ApexHAB/apex-iii/core/pcb/rev1.0/apex-iii-core-brd.png

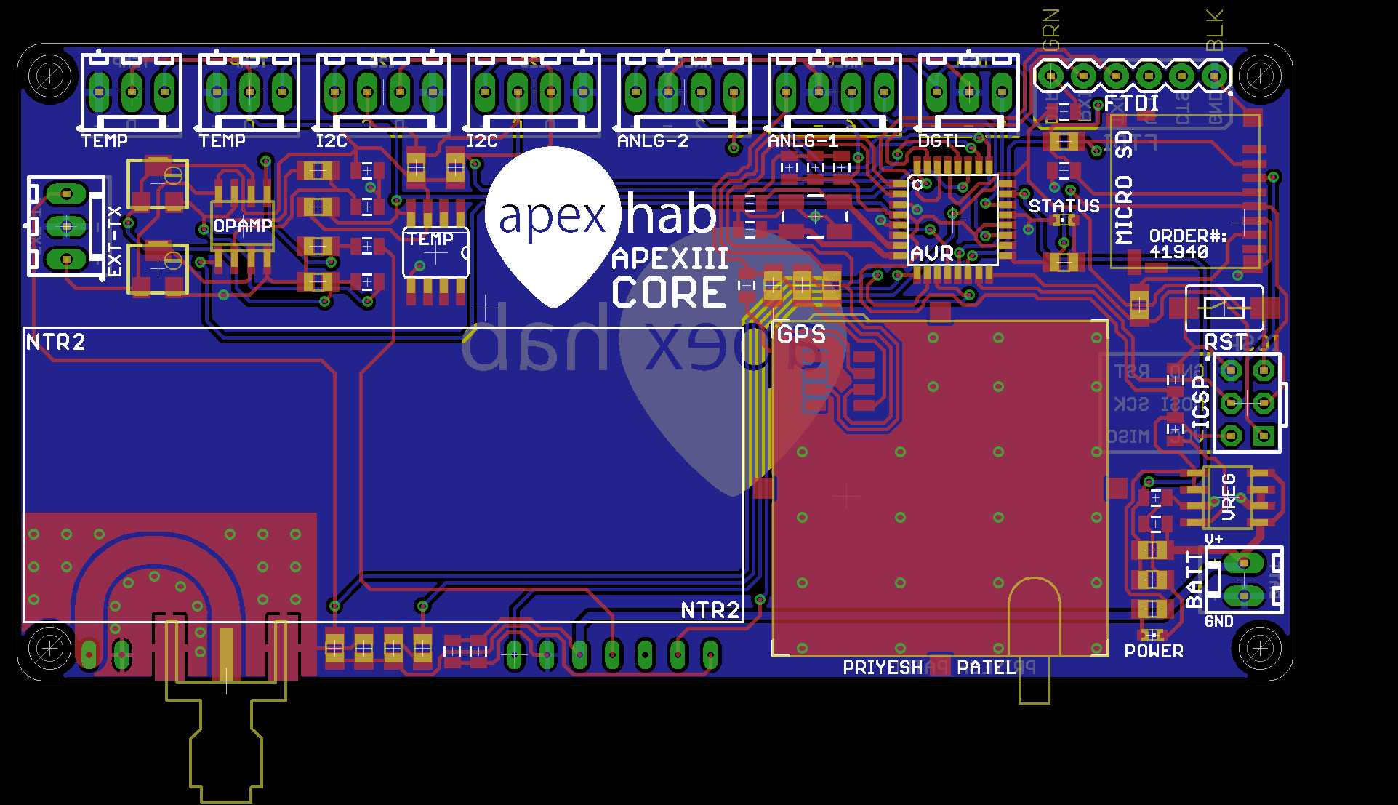
core/pcb/rev1.0/apex-iii-core-brd.png
