ApexHAB/apex-iii/core/pcb/rev1.0/apex-iii-core-sch.png

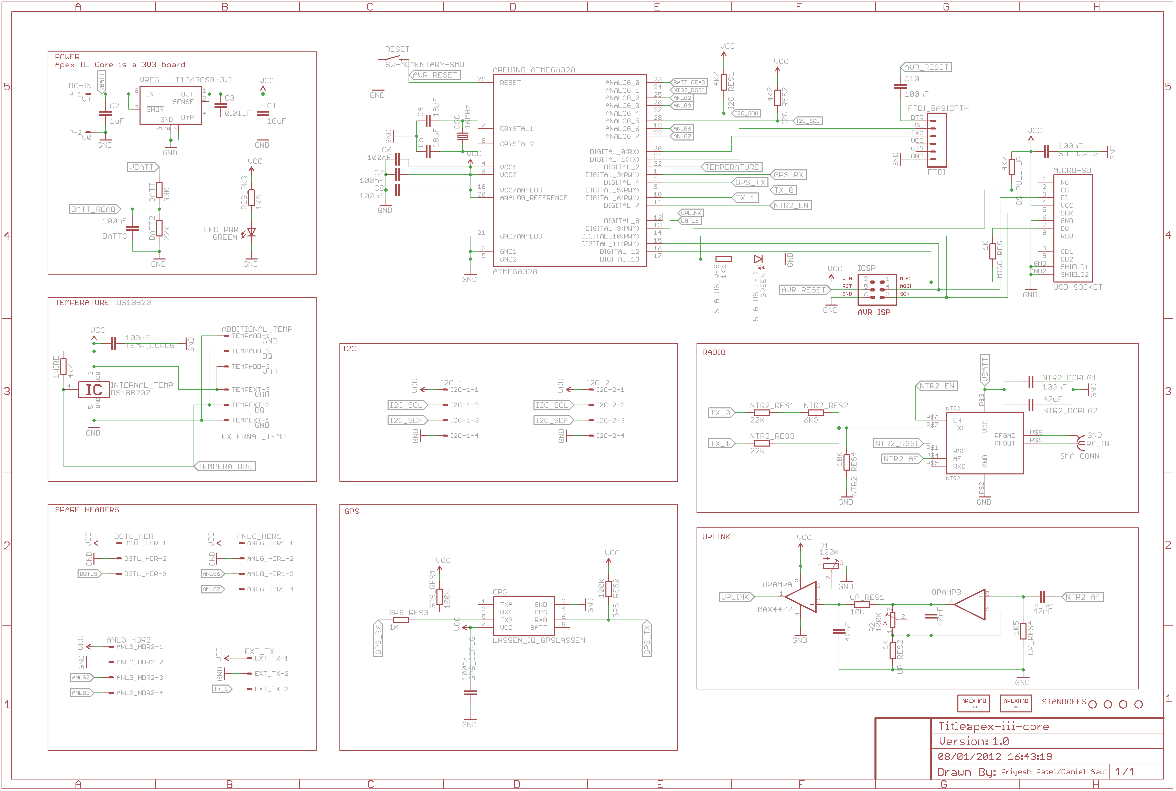
core/pcb/rev1.0/apex-iii-core-sch.png
