ApexHAB/apex-iii/launches/launch-1/track/apex-iii-l1-track-1.png

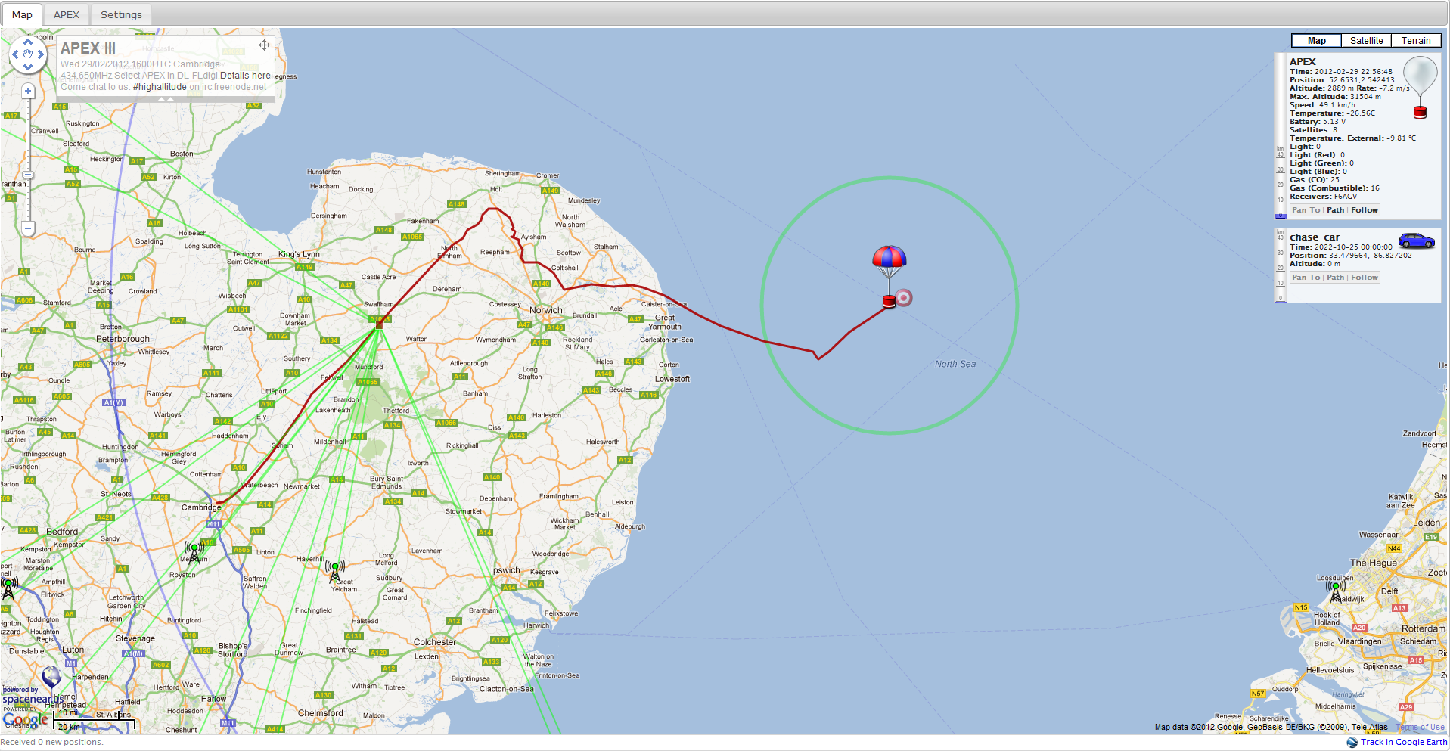
launches/launch-1/track/apex-iii-l1-track-1.png
