ApexHAB/apex-iii/launches/launch-1/track/apex-iii-l1-track-5.png

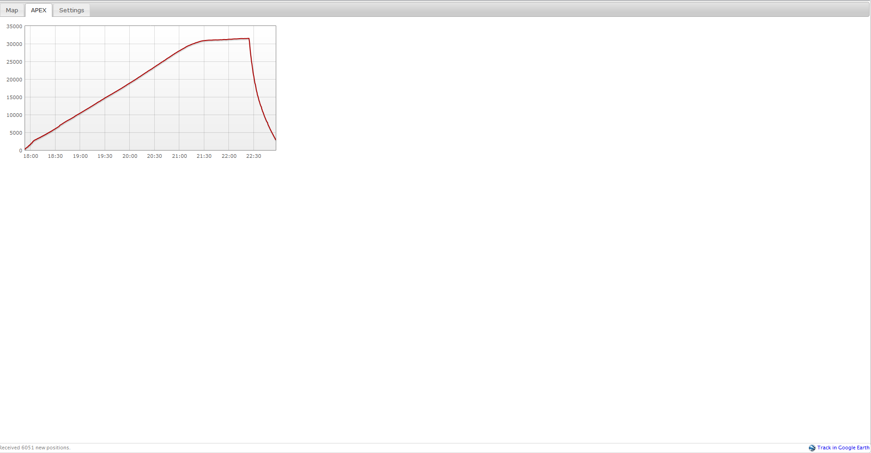
launches/launch-1/track/apex-iii-l1-track-5.png
