ApexHAB/apex-iii/launches/launch-2/track/ApexIIILaunch2-Track (2).png

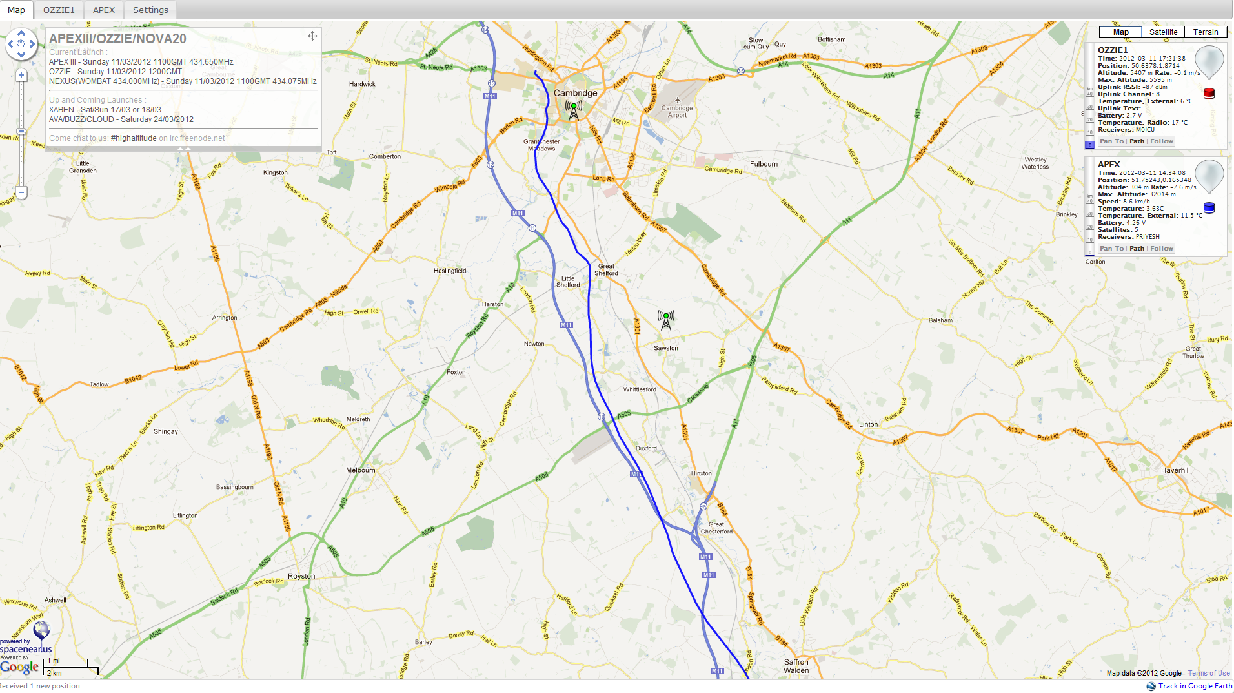
launches/launch-2/track/ApexIIILaunch2-Track (2).png
