ApexHAB/apex-iii/modules/adc_lemon/pcb/adc-lemon-sch.png

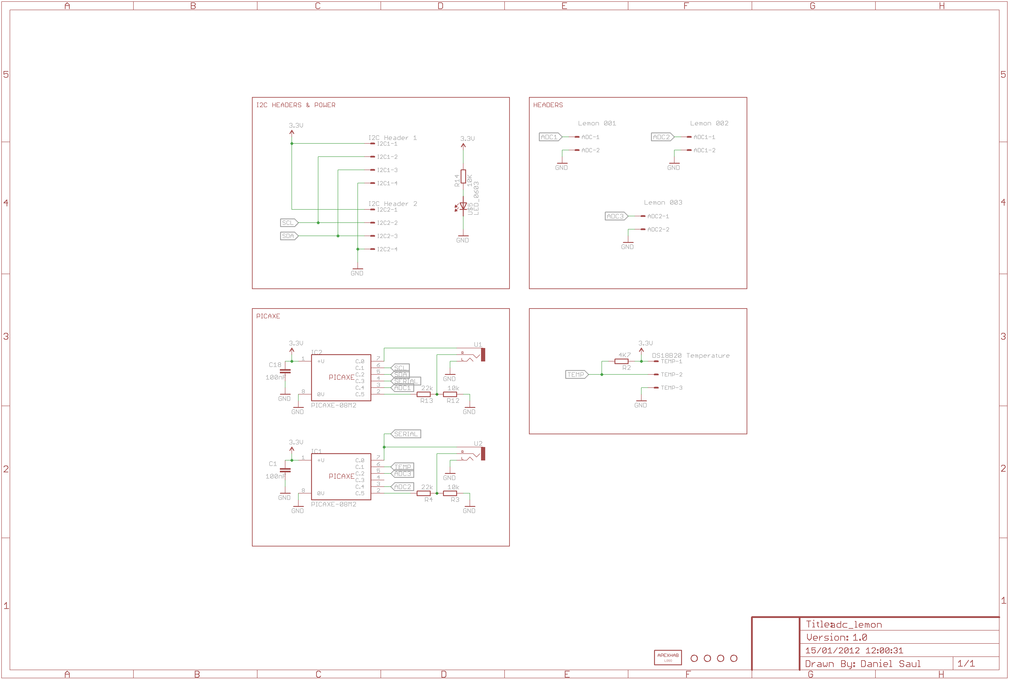
modules/adc_lemon/pcb/adc-lemon-sch.png
