ApexHAB/apex-iii/modules/light/pcb/light-brd.png

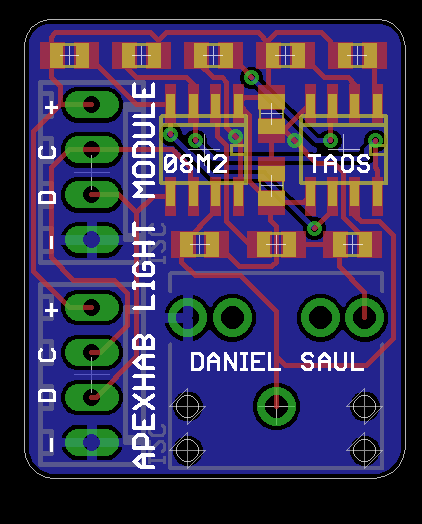
modules/light/pcb/light-brd.png
