ApexHAB/apex-iii/modules/light/pcb/light-sch.png

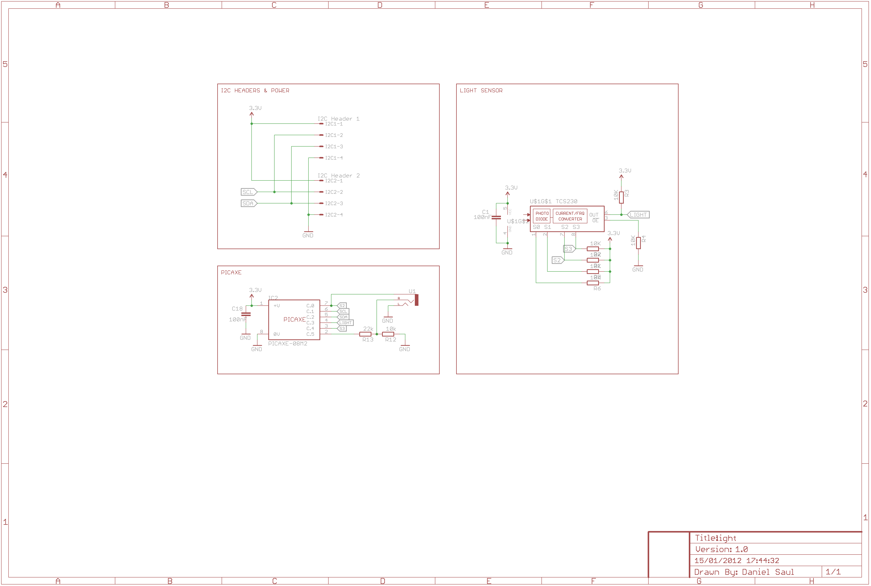
modules/light/pcb/light-sch.png
