ApexHAB/apex-iii/modules/pressure_humidity/pcb-balloon/pressure-balloon-brd.png

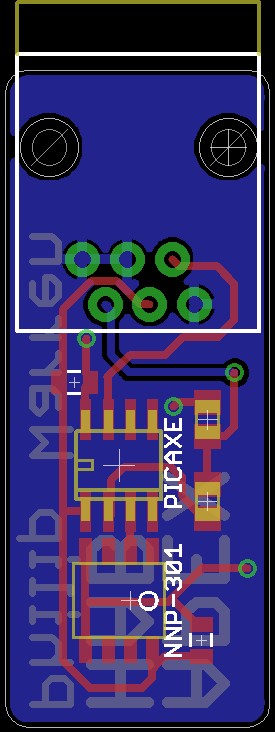
modules/pressure_humidity/pcb-balloon/pressure-balloon-brd.png
