ApexHAB/apex-iii/modules/pressure_humidity/pcb-balloon/pressure-balloon-sch.png

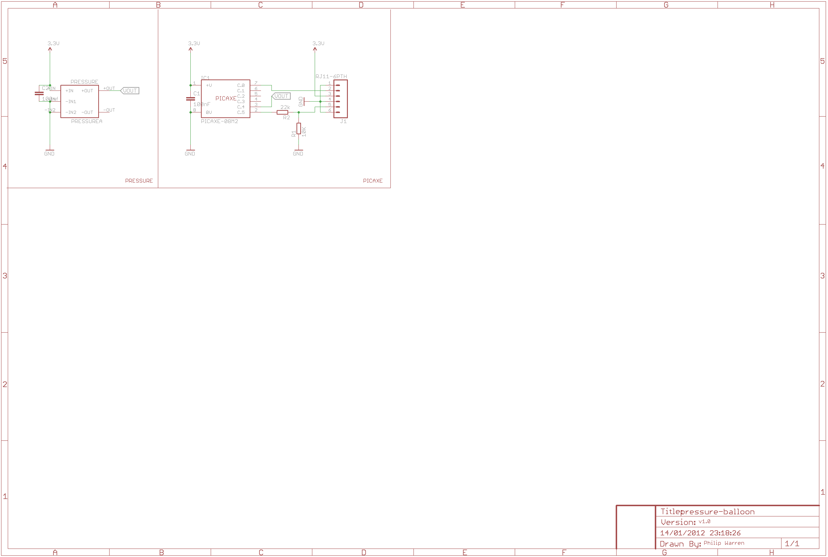
modules/pressure_humidity/pcb-balloon/pressure-balloon-sch.png
