ApexHAB/apex-iii/modules/pressure_humidity/pcb-main/pressure-humidity-main-brd.png

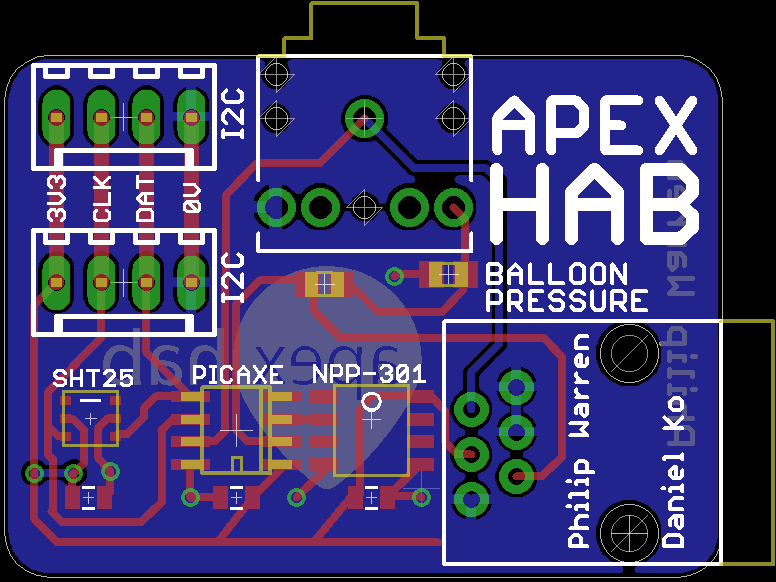
modules/pressure_humidity/pcb-main/pressure-humidity-main-brd.png
