ApexHAB/apex-iii/modules/pressure_humidity/pcb-main/pressure-humidity-main-sch.png

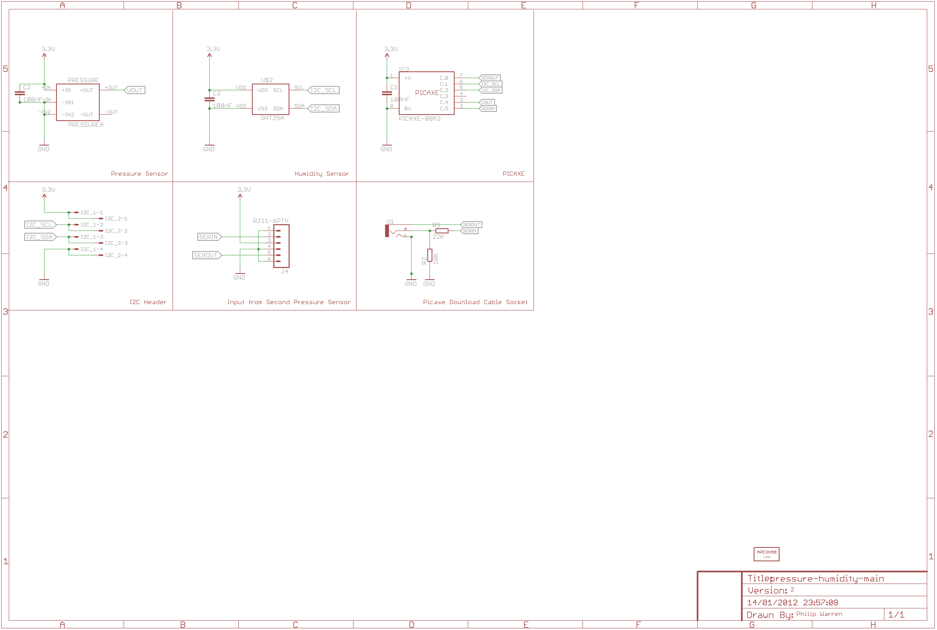
modules/pressure_humidity/pcb-main/pressure-humidity-main-sch.png
