ApexHAB/apex-iii/modules/radiation/pcb/radiation-brd.png

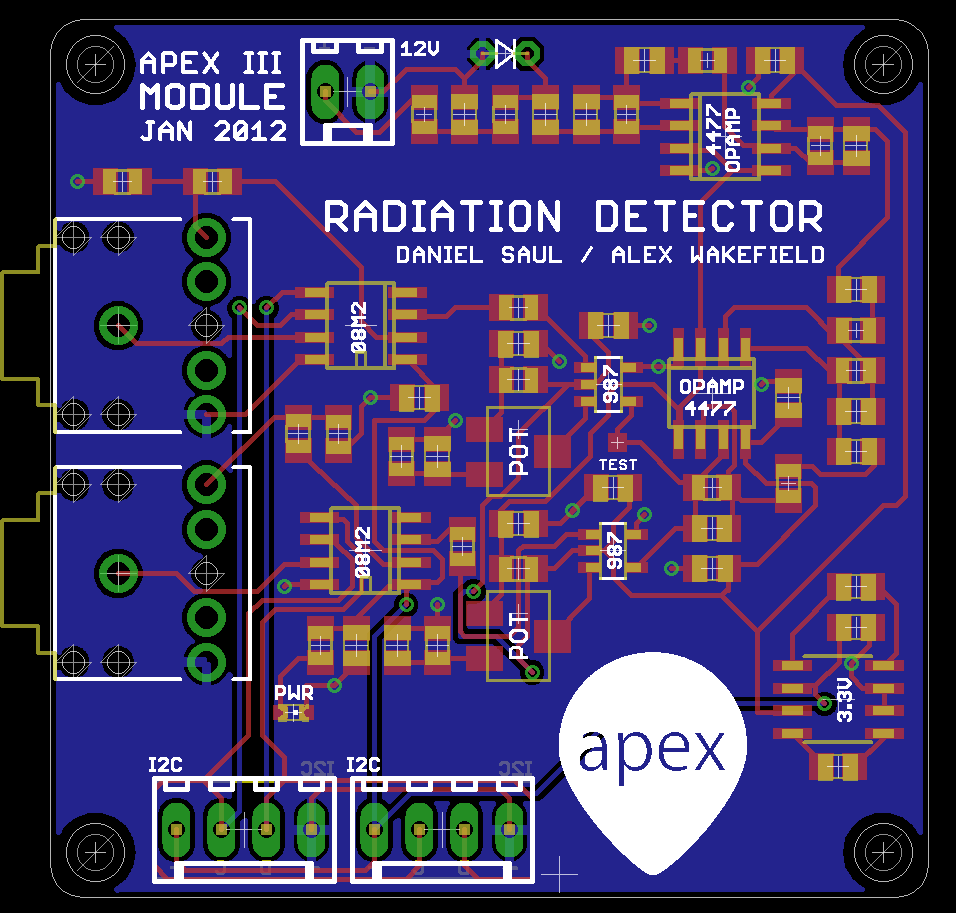
modules/radiation/pcb/radiation-brd.png
