ApexHAB/apex-iii/modules/radiation/pcb/radiation-sch.png

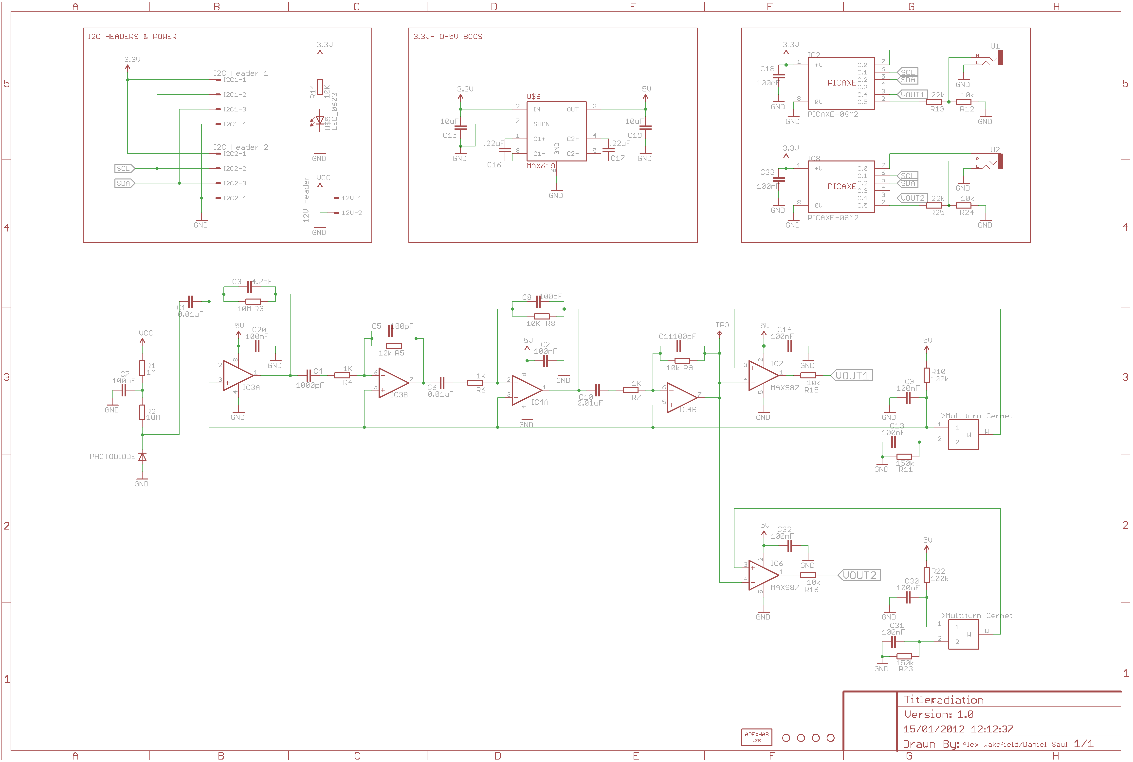
modules/radiation/pcb/radiation-sch.png
