ApexHAB/apex-iii/modules/siren_cutdown/pcb/siren-cutdown-sch.png

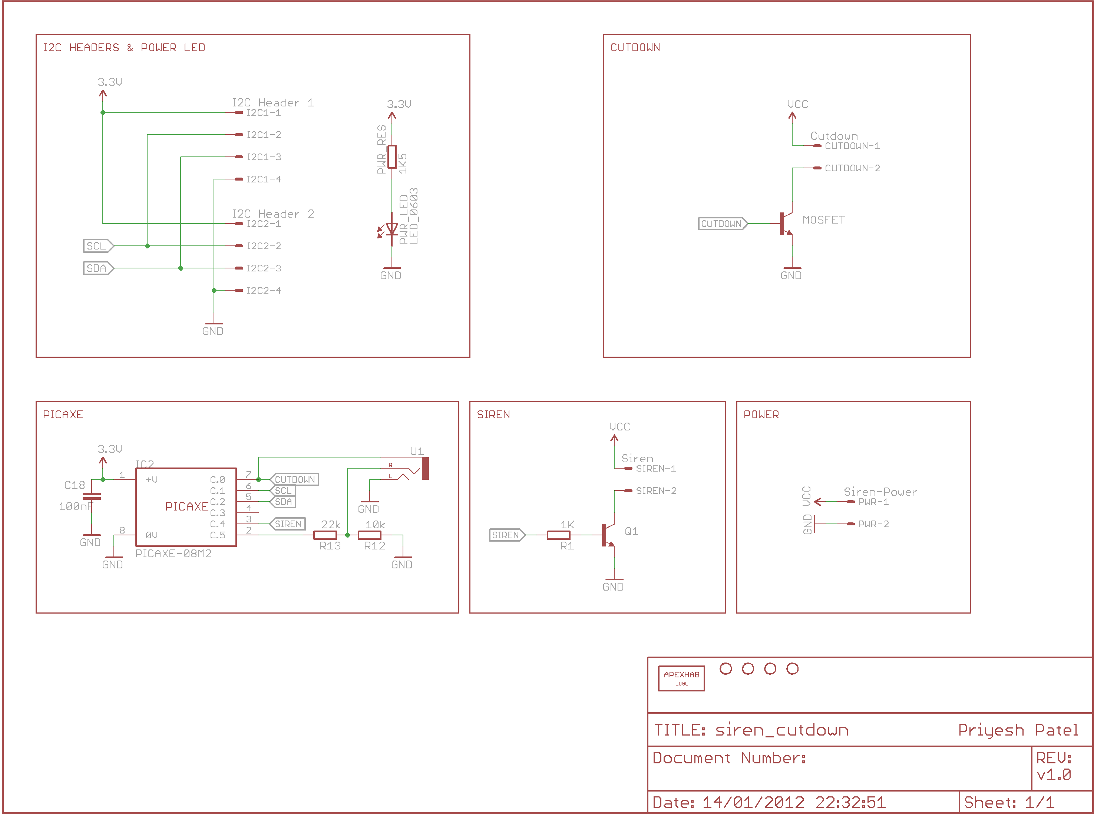
modules/siren_cutdown/pcb/siren-cutdown-sch.png
