ApexHAB/apex-iii/modules/tilt_control/pcb/tiltcontrol-brd.png

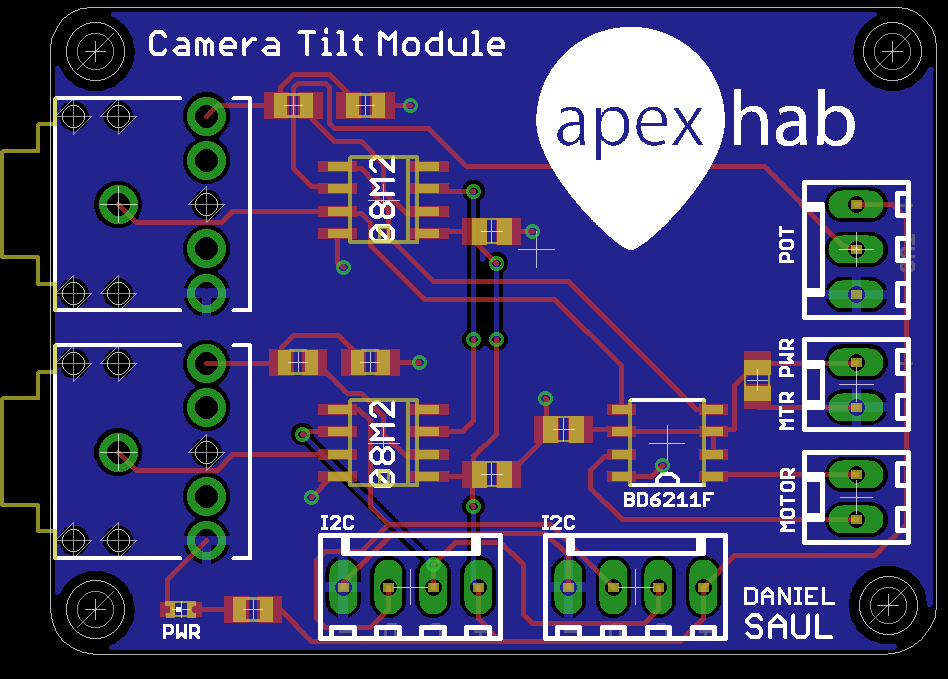
modules/tilt_control/pcb/tiltcontrol-brd.png
