ApexHAB/apex-iii/modules/tilt_control/pcb/tiltcontrol-sch.png

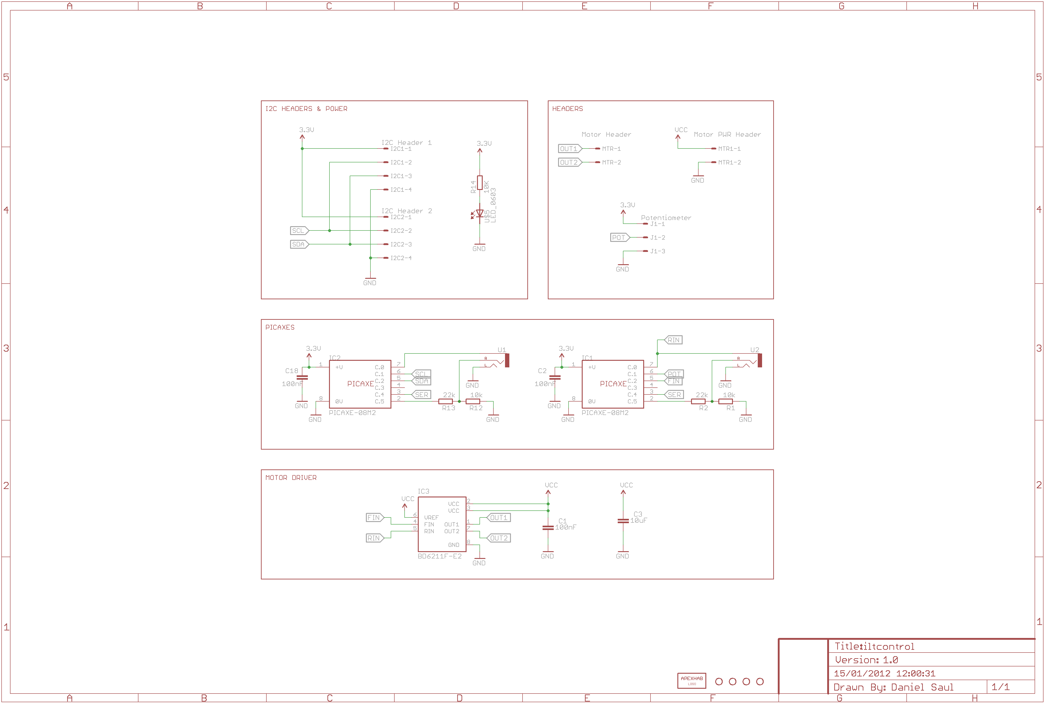
modules/tilt_control/pcb/tiltcontrol-sch.png
